jaydenaleung/helioHydration/filter/cad/production/render-6.png

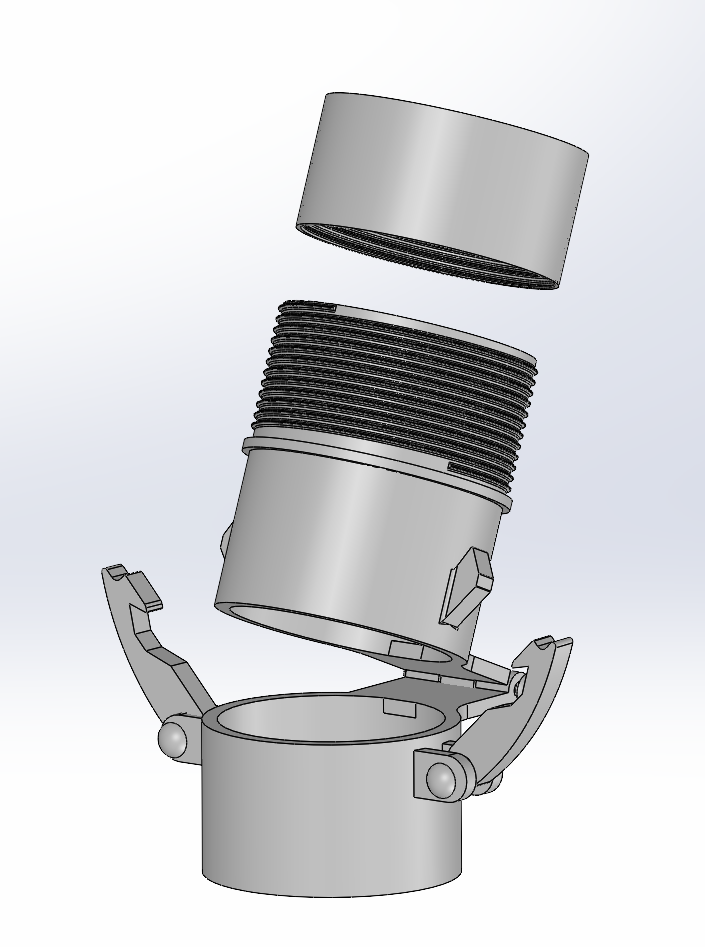
filter/cad/production/render-6.png
