jaydenaleung/helioHydration/filter/cad/production/render-8.png

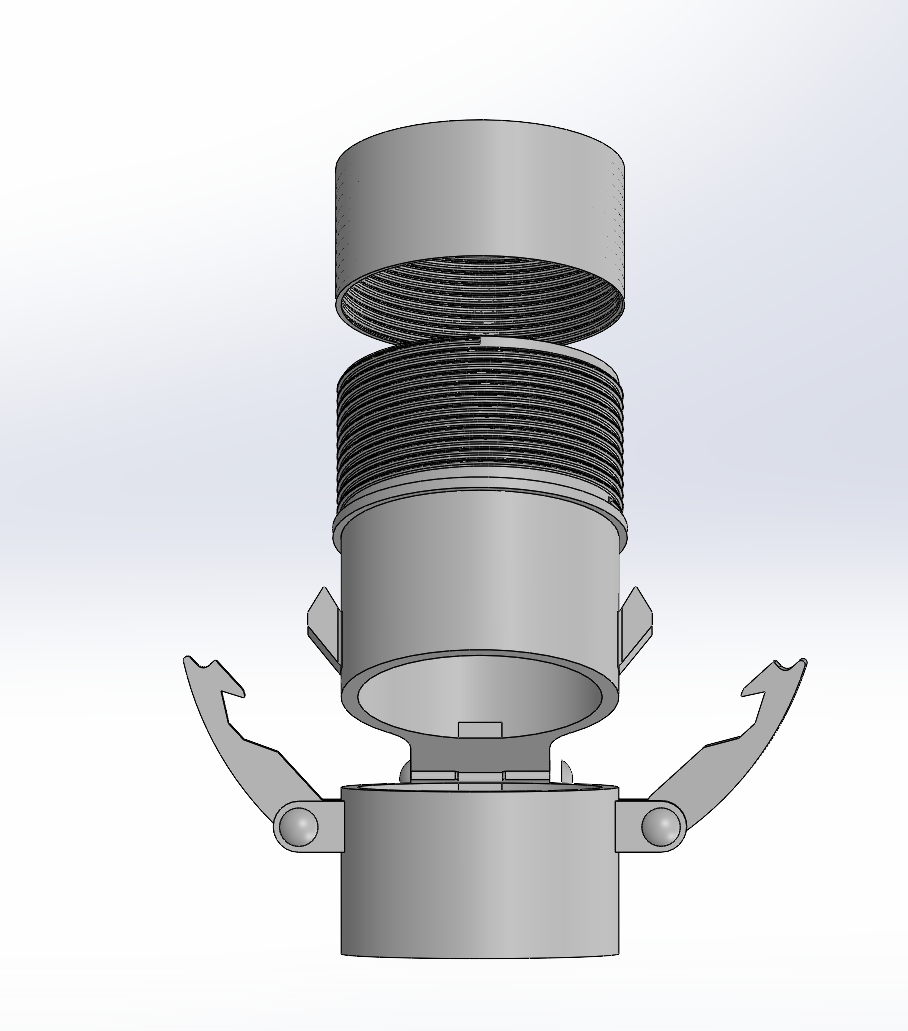
filter/cad/production/render-8.png
