jaydenaleung/helioHydration/filter/cad/hinge_assempreview_notneeded.SLDASM

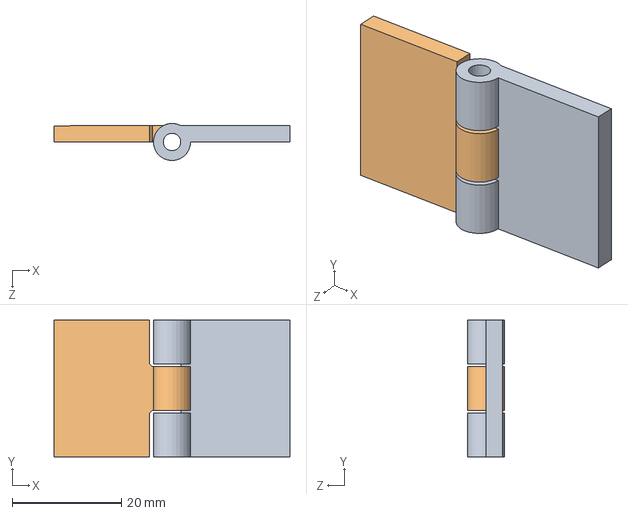
[picture p11: CAD file, 2026-01-02]
filter/cad/hinge_assempreview_notneeded.SLDASM
43.2 x 25.0 x 6.80 mm
hinge_2
hinge_1
