jaydenaleung/helioHydration/indicator/cad/Body1.SLDPRT

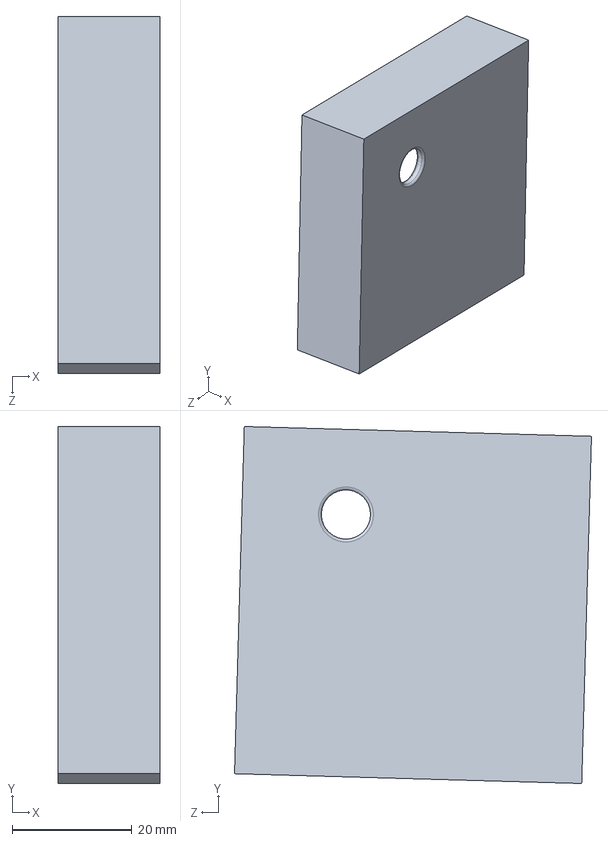
[picture p24: CAD file, 2026-01-12]
indicator/cad/Body1.SLDPRT
17.0 x 59.6 x 59.6 mm
