jaydenaleung/helioHydration/indicator/cad/refs/models/helioHydration_indicator_pcb.step

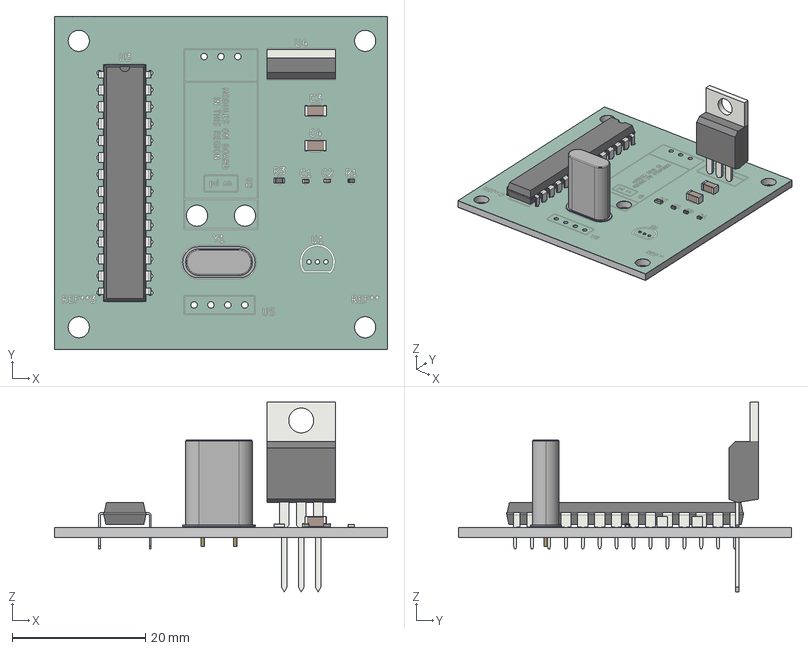
[picture p25: CAD file, 2026-01-04]
indicator/cad/refs/models/helioHydration_indicator_pcb.step
50.0 x 50.0 x 28.5 mm
C_0402_1005Metric x 2
TO-220-3_Vertical
C_1206_3216Metric x 2
R_0402_1005Metric
DIP-28_W7.62mm
R_0603_1608Metric
Crystal_HC49-U_Vertical
helioHydration_indicator_silkscreen
helioHydration_indicator_soldermask
helioHydration_indicator_PCB
