jaydenaleung/helioHydration/filter/cad/body_2.SLDPRT

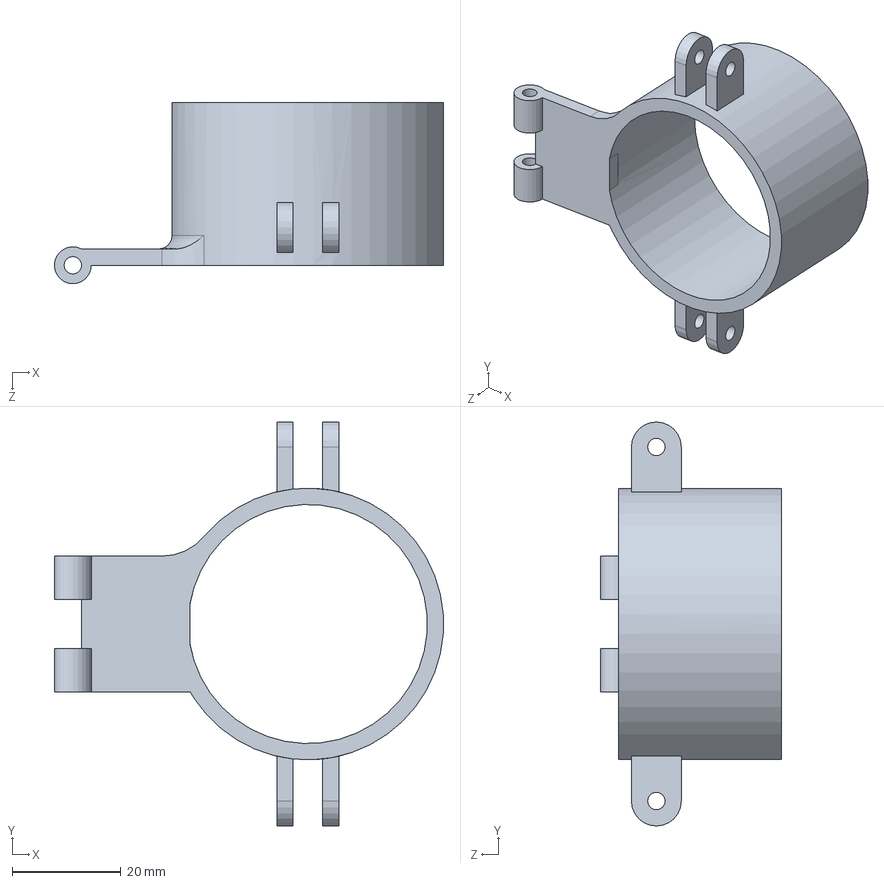
[picture p26: CAD file, 2026-01-02]
filter/cad/body_2.SLDPRT
71.6 x 74.4 x 33.4 mm
