jaydenaleung/helioHydration/indicator/cad/standoff.SLDPRT

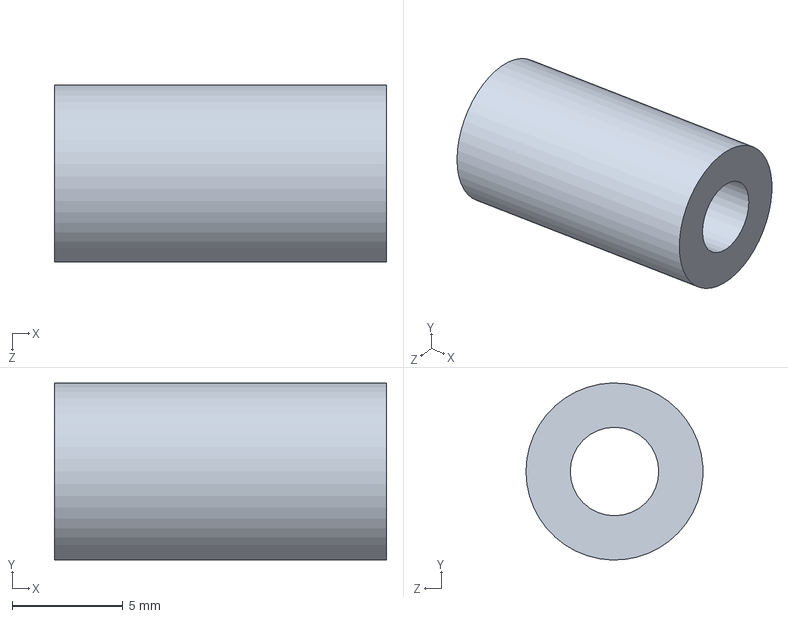
[picture p27: CAD file, 2026-01-05]
indicator/cad/standoff.SLDPRT
15.0 x 8.00 x 8.00 mm
