jaydenaleung/helioHydration/filter/cad/clip_pin.SLDPRT

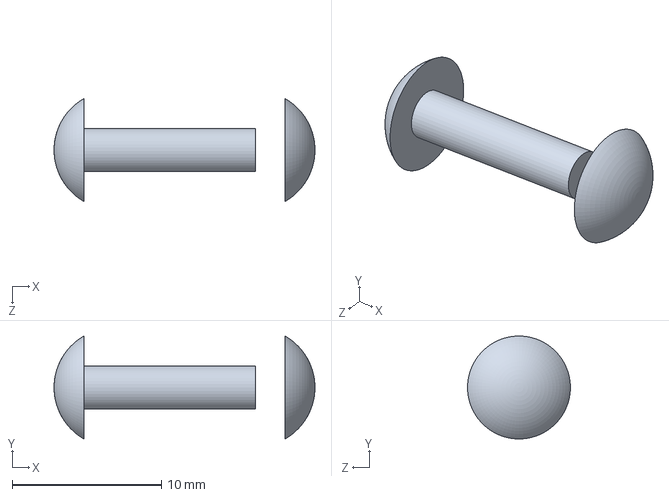
[picture p28: CAD file, 2026-01-02]
filter/cad/clip_pin.SLDPRT
17.5 x 6.90 x 6.90 mm
