jaydenaleung/helioHydration/filter/cad/body_1.SLDPRT

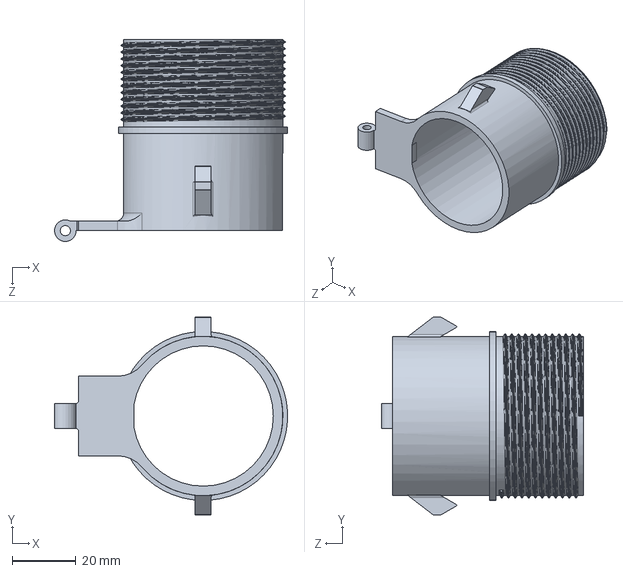
[picture p29: CAD file, 2026-01-02]
filter/cad/body_1.SLDPRT
73.1 x 62.0 x 63.4 mm
