jaydenaleung/helioHydration/filter/cad/clip.SLDPRT

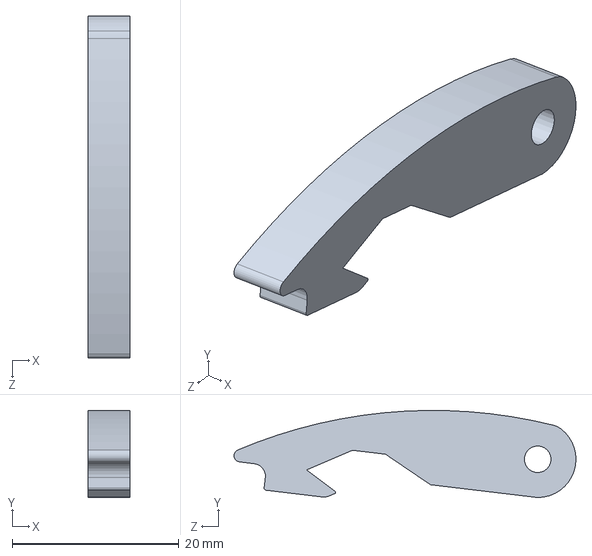
[picture p30: CAD file, 2026-01-02]
filter/cad/clip.SLDPRT
5.00 x 10.5 x 41.1 mm
