jaydenaleung/helioHydration/filter/cad/hinge_pin.SLDPRT

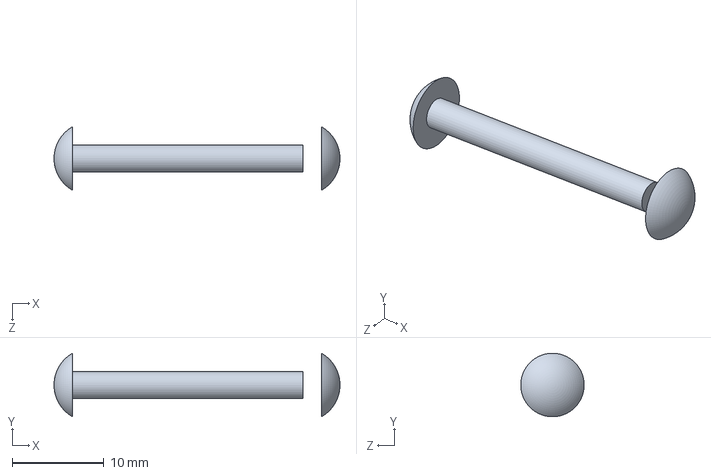
[picture p31: CAD file, 2026-01-02]
filter/cad/hinge_pin.SLDPRT
31.1 x 6.90 x 6.90 mm
