jaydenaleung/helioHydration/filter/cad/hinge_1.SLDPRT

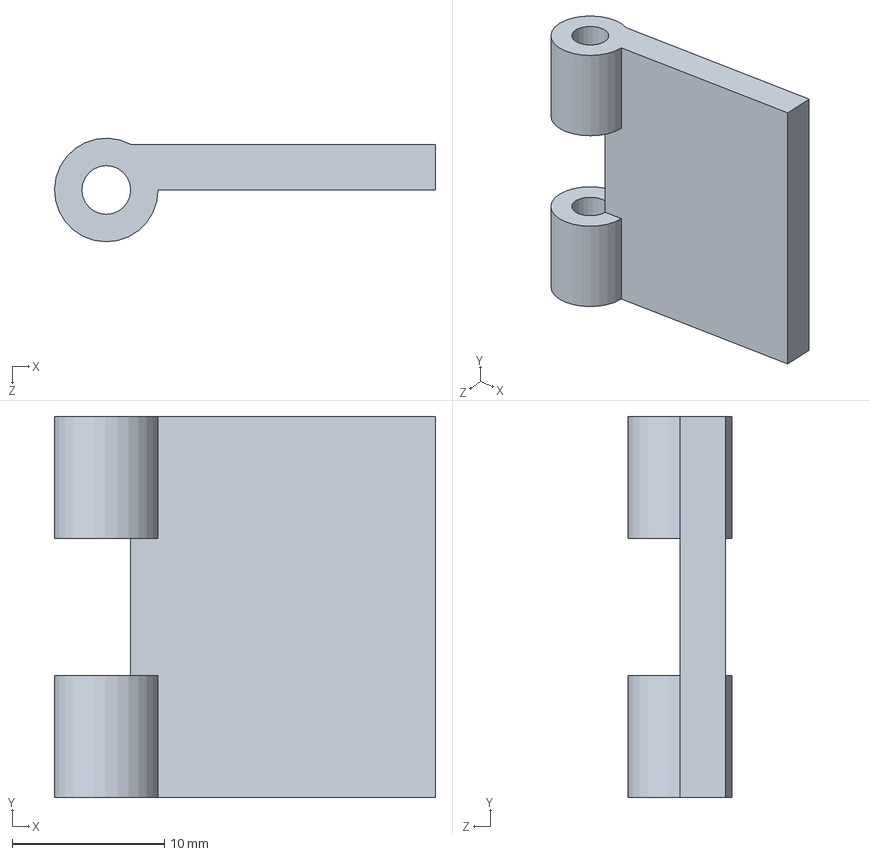
[picture p32: CAD file, 2026-01-02]
filter/cad/hinge_1.SLDPRT
25.0 x 25.0 x 6.80 mm
